DataRaidersMMM/ALMA/ESUQUEMAELECTRICO/pastilleroEsquema.JPG

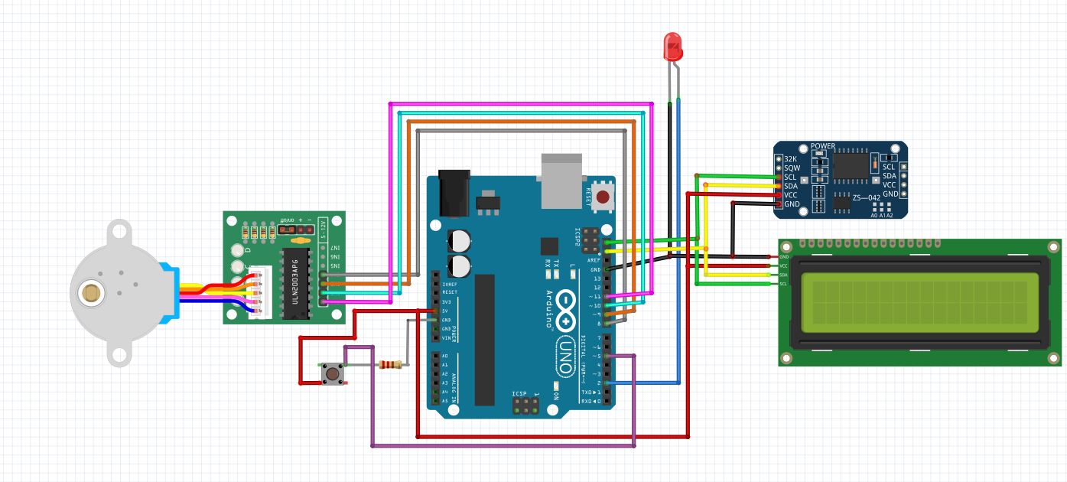
ESUQUEMAELECTRICO/pastilleroEsquema.JPG
