DataRaidersMMM/ALMA/ESUQUEMAELECTRICO/robotEsquema.JPG

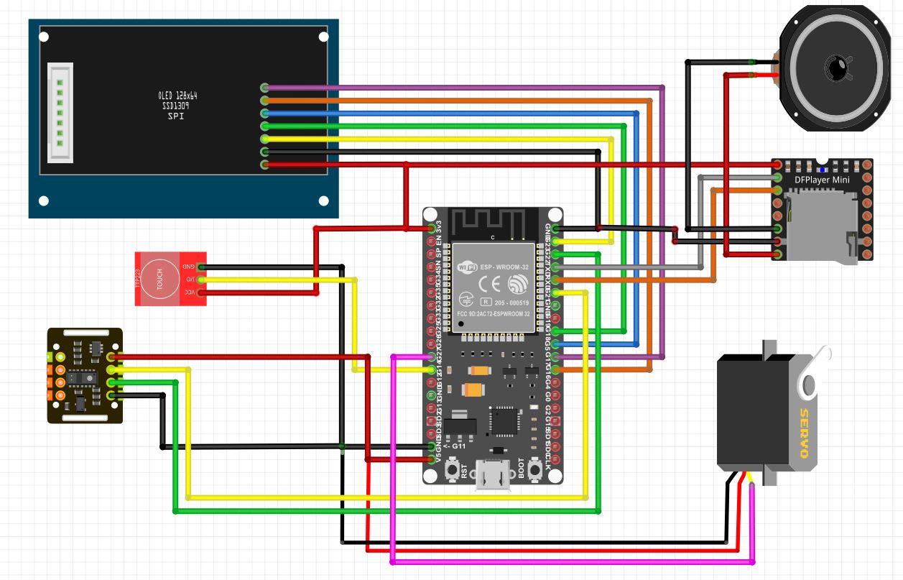
ESUQUEMAELECTRICO/robotEsquema.JPG
