DataRaidersMMM/ALMA/IMAGES/FINAL_NACIONAL/c0f74e2c-b573-4f79-add3-1c2ad05ea93c.jpg

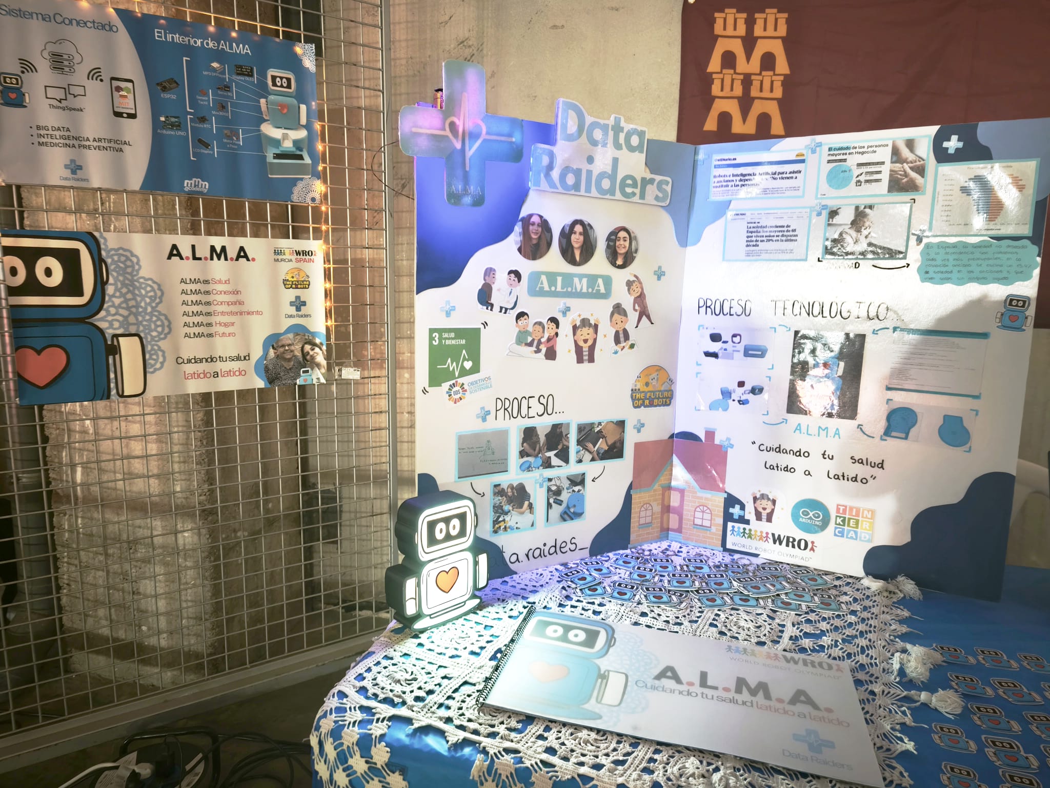
IMAGES/FINAL_NACIONAL/c0f74e2c-b573-4f79-add3-1c2ad05ea93c.jpg
