DataRaidersMMM/ALMA/IMAGES/FINAL_NACIONAL/daf87f93-81f6-4190-b653-e9413617f9fc.jpg

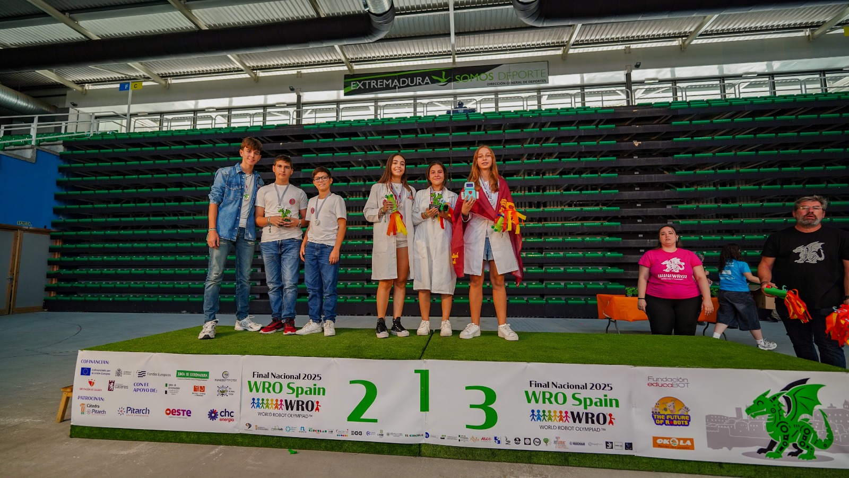
IMAGES/FINAL_NACIONAL/daf87f93-81f6-4190-b653-e9413617f9fc.jpg
