DataRaidersMMM/ALMA/IMAGES/FINAL_NACIONAL/WhatsApp Image 2025-09-20 at 20.38.06.jpg

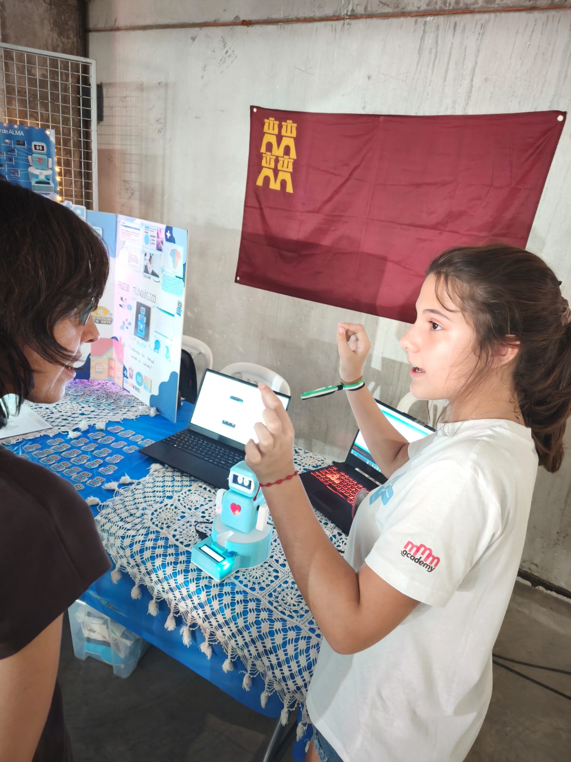
IMAGES/FINAL_NACIONAL/WhatsApp Image 2025-09-20 at 20.38.06.jpg
