DataRaidersMMM/ALMA/IMAGES/FINAL_NACIONAL/WhatsApp Image 2025-09-22 at 10.02.04.jpg

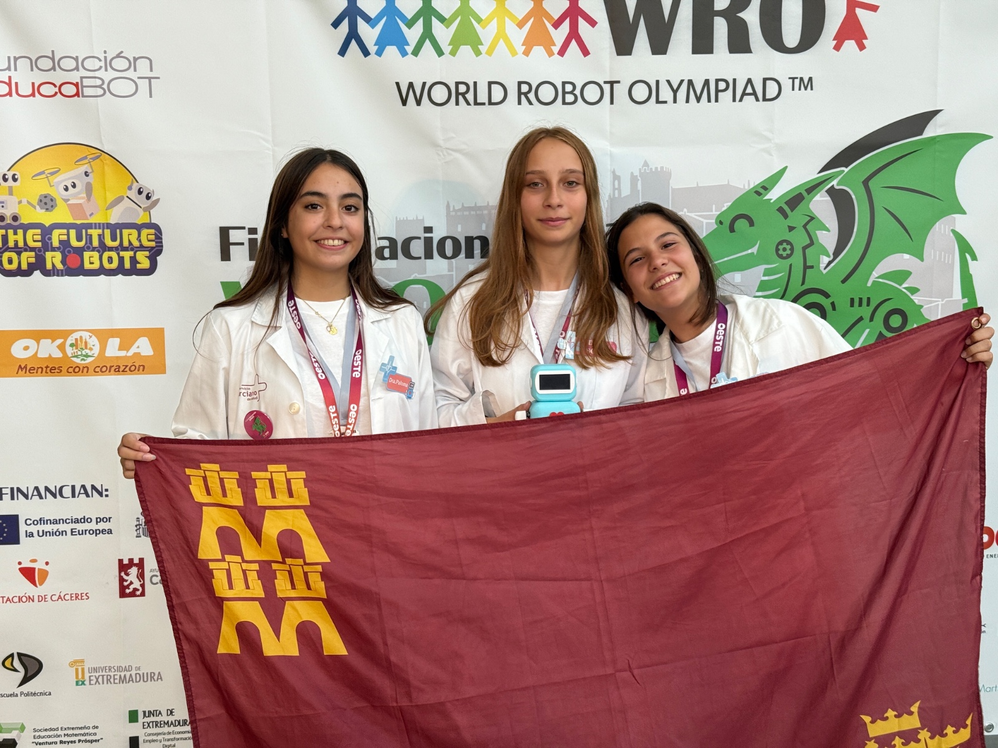
IMAGES/FINAL_NACIONAL/WhatsApp Image 2025-09-22 at 10.02.04.jpg
