DataRaidersMMM/ALMA/IMAGES/FINAL_NACIONAL/WhatsApp Image 2025-09-22 at 13.36.57 (1).jpg

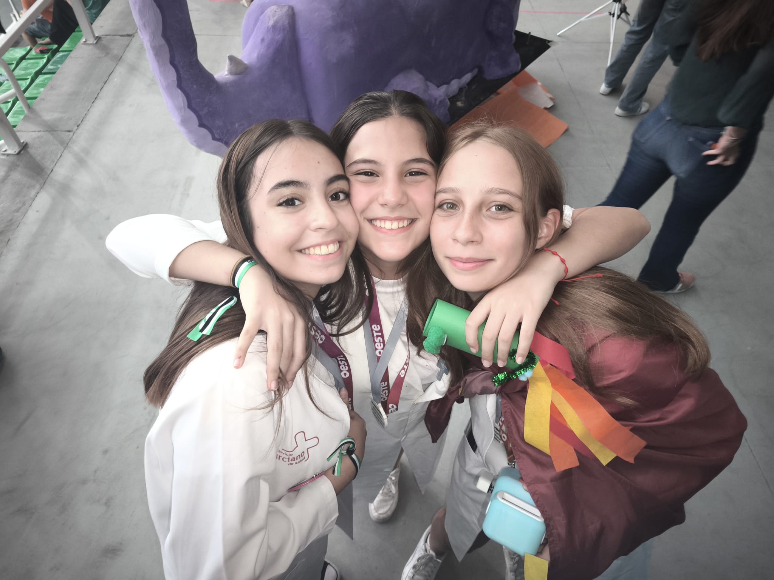
IMAGES/FINAL_NACIONAL/WhatsApp Image 2025-09-22 at 13.36.57 (1).jpg
