DataRaidersMMM/ALMA/IMAGES/FINAL_NACIONAL/WhatsApp Image 2025-09-22 at 13.37.01 (2).jpg

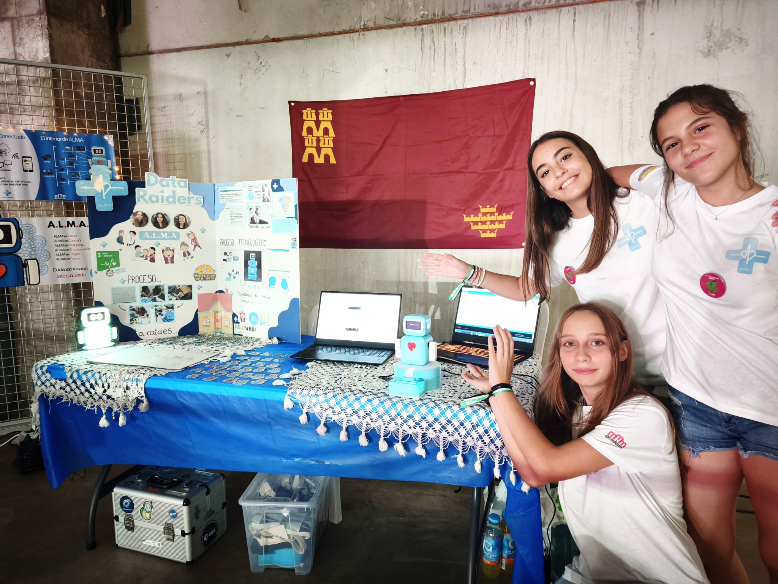
IMAGES/FINAL_NACIONAL/WhatsApp Image 2025-09-22 at 13.37.01 (2).jpg
