DataRaidersMMM/ALMA/IMAGES/Robot azul con corazón rojo (1).png

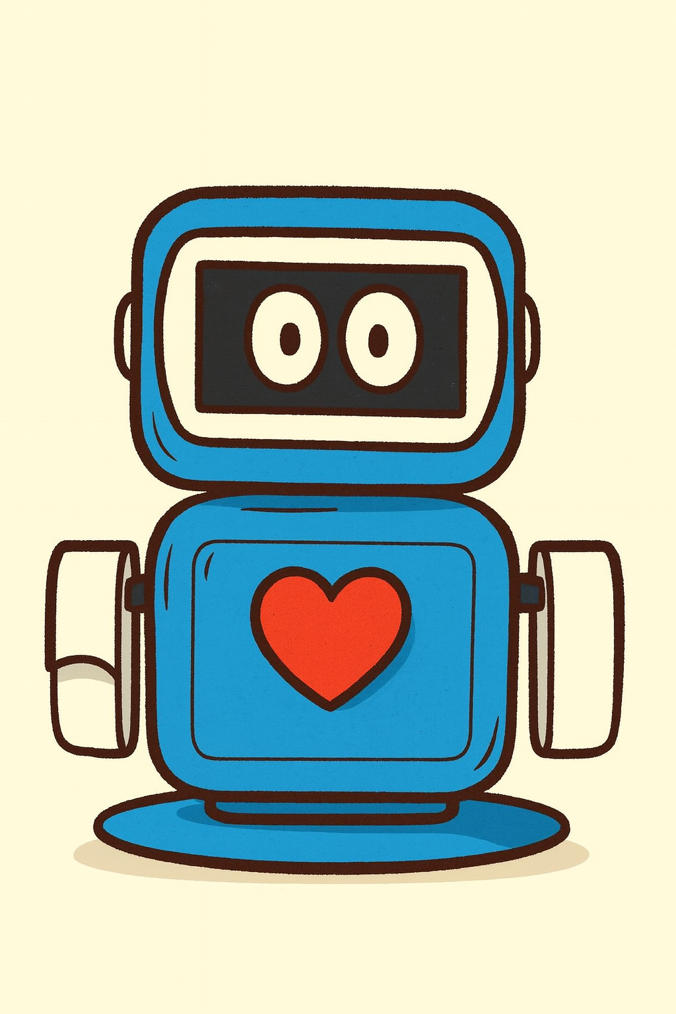
IMAGES/Robot azul con corazón rojo (1).png
