DataRaidersMMM/ALMA/IMAGES/VISITS/1757670545901.jpg

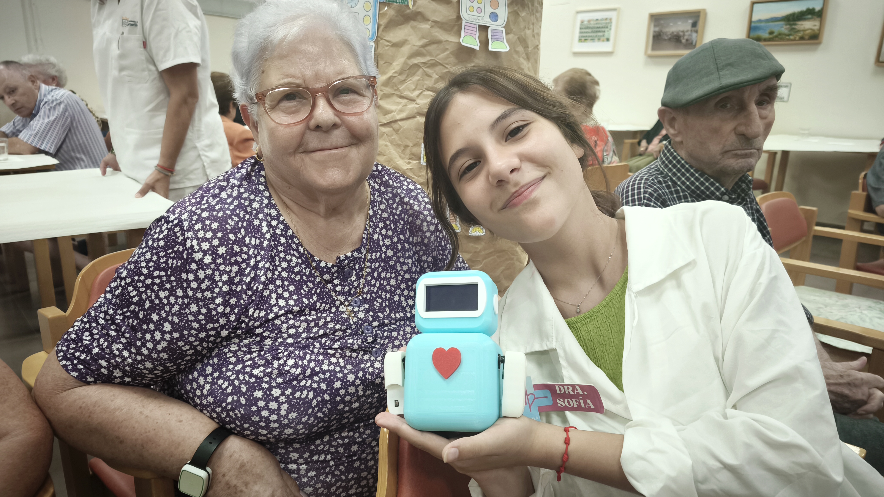
IMAGES/VISITS/1757670545901.jpg
