DataRaidersMMM/ALMA/IMAGES/VISITS/1757670545951.jpg

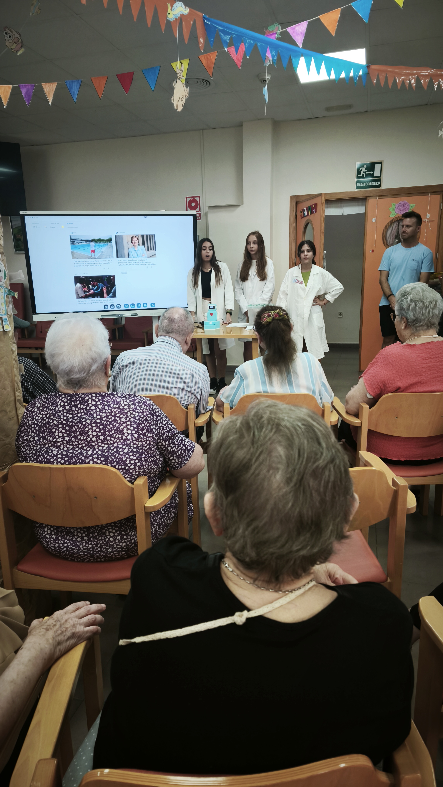
IMAGES/VISITS/1757670545951.jpg
