DataRaidersMMM/ALMA/IMAGES/VISITS/1757670545973.jpg

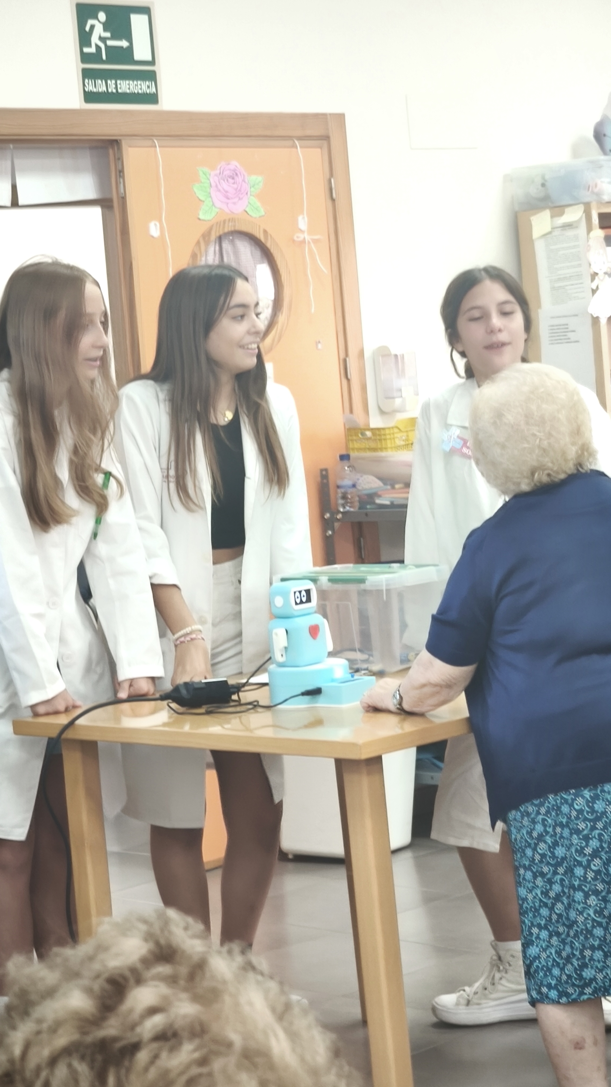
IMAGES/VISITS/1757670545973.jpg
