DataRaidersMMM/ALMA/IMAGES/VISITS/1757670794867.jpg

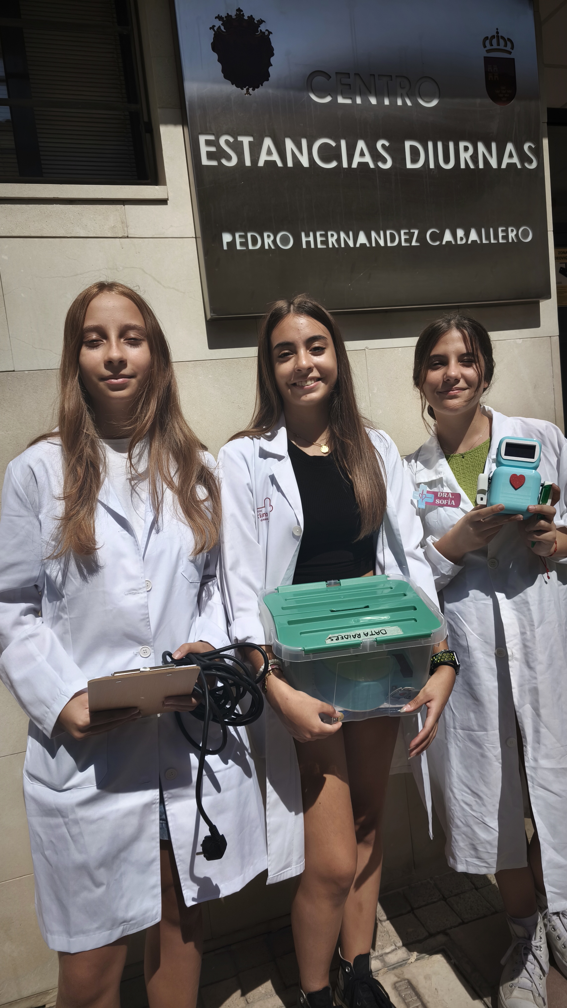
IMAGES/VISITS/1757670794867.jpg
