DataRaidersMMM/ALMA/IMAGES/VISITS/1757670794919.jpg

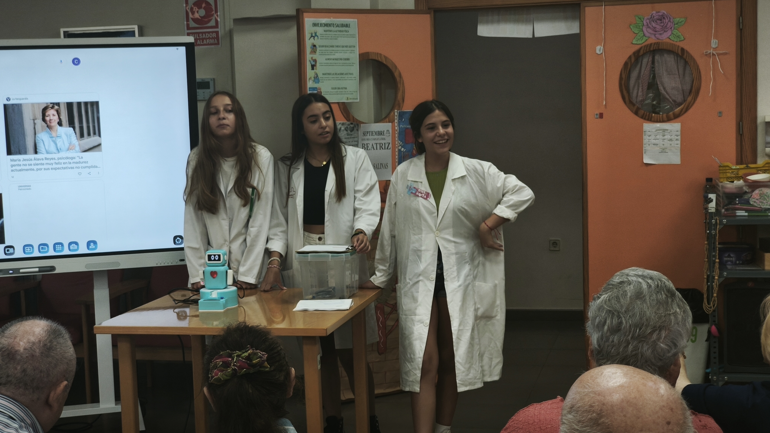
IMAGES/VISITS/1757670794919.jpg
