DataRaidersMMM/ALMA/IMAGES/VISITS/1757670794963.jpg

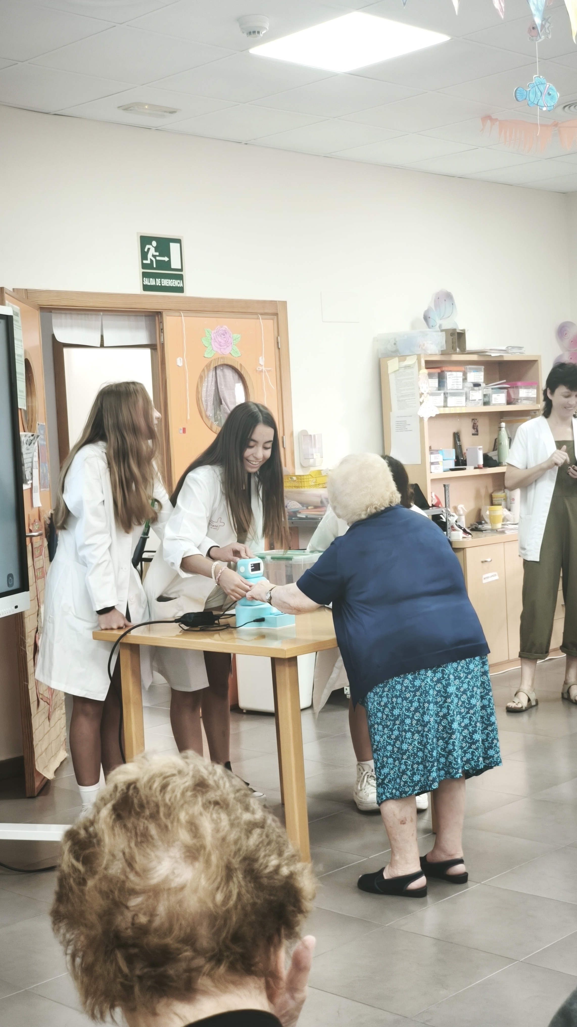
IMAGES/VISITS/1757670794963.jpg
