DataRaidersMMM/ALMA/IMAGES/VISITS/1757670794984.jpg

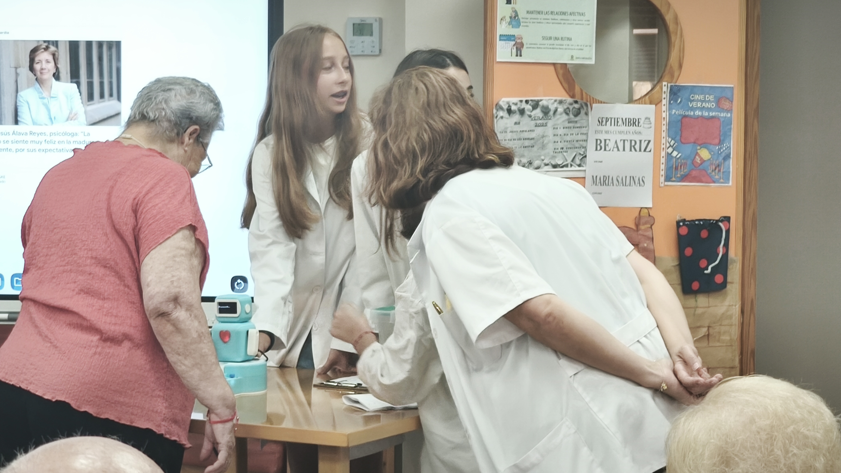
IMAGES/VISITS/1757670794984.jpg
