DataRaidersMMM/ALMA/IMAGES/VISITS/1757670795003.jpg

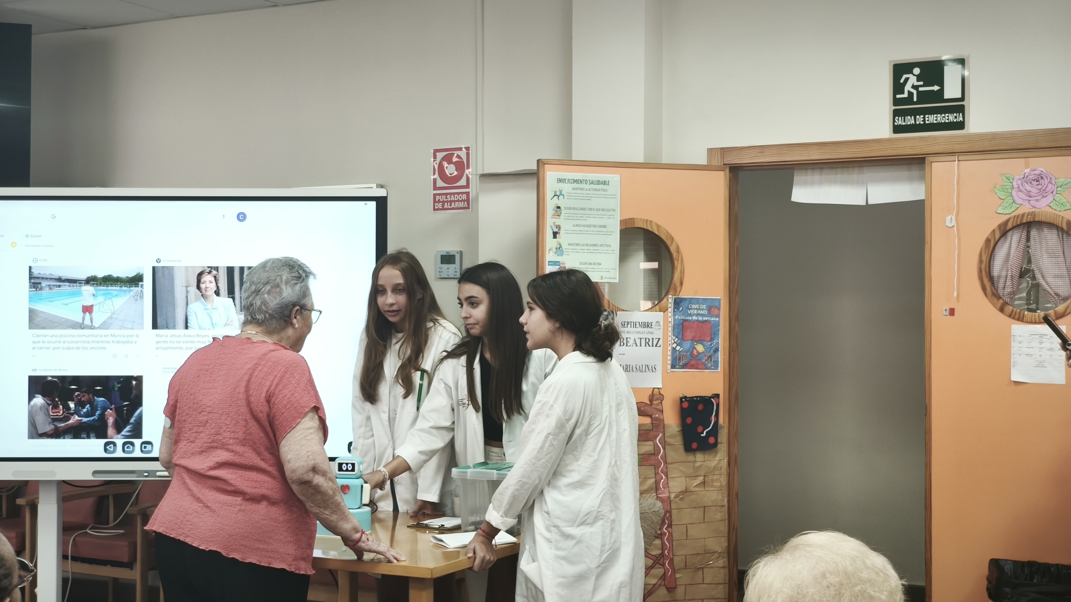
IMAGES/VISITS/1757670795003.jpg
