DataRaidersMMM/ALMA/IMAGES/VISITS/1757670795028.jpg

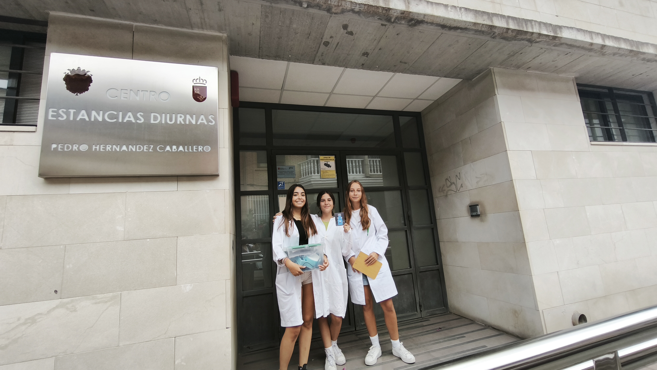
IMAGES/VISITS/1757670795028.jpg
