DataRaidersMMM/ALMA/STL/PASTILLERO/contenedor.stl

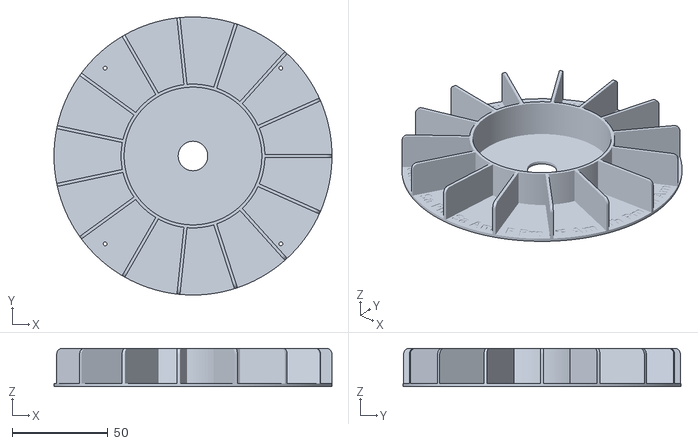
[picture p40: CAD file, 2025-10-04]
STL/PASTILLERO/contenedor.stl
145.0 x 145.0 x 20.0
