DataRaidersMMM/ALMA/STL/ROBOT/oreja.stl

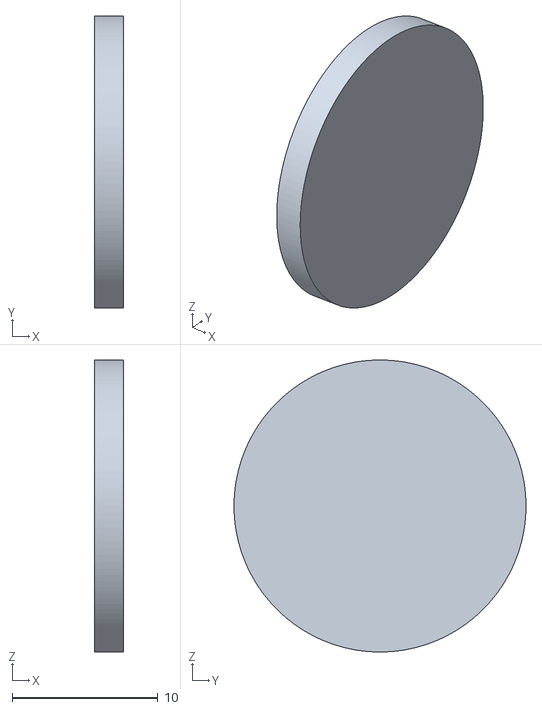
[picture p41: CAD file, 2025-10-04]
STL/ROBOT/oreja.stl
2.00 x 20.0 x 20.0
