DataRaidersMMM/ALMA/STL/ROBOT/parte1cabeza.stl

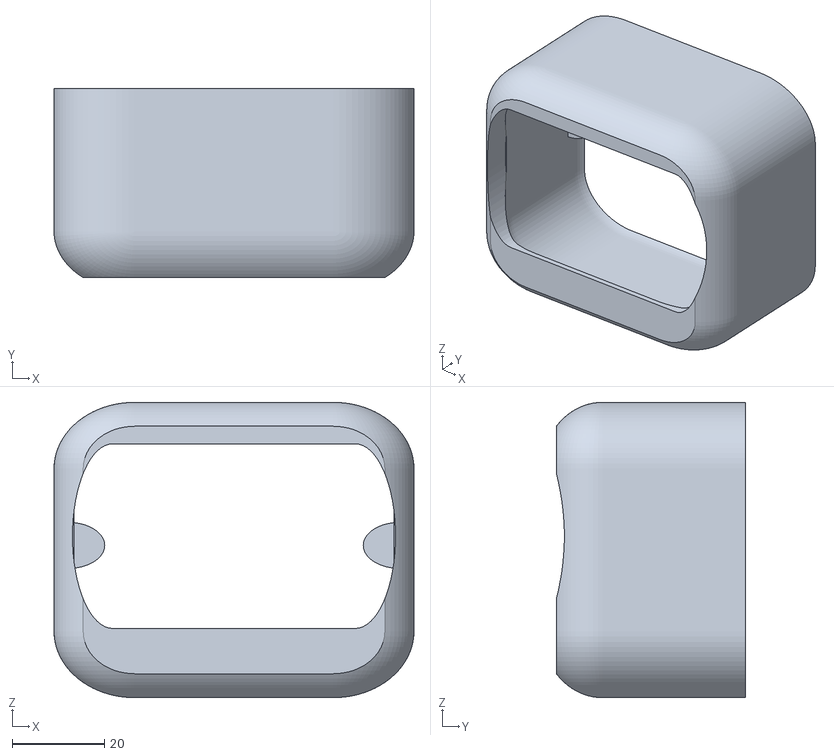
[picture p42: CAD file, 2025-10-04]
STL/ROBOT/parte1cabeza.stl
78.0 x 41.0 x 64.0
